POJFM/dmp-plant-hub/docs/final-report-sikora/img/web-ui-pump.png

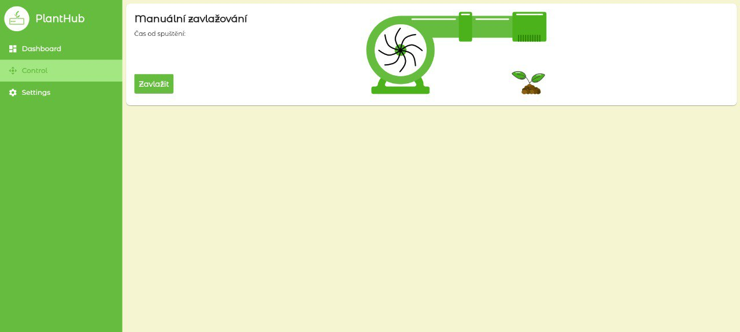
docs/final-report-sikora/img/web-ui-pump.png
