POJFM/dmp-plant-hub/docs/schemas/circuit-schema.png

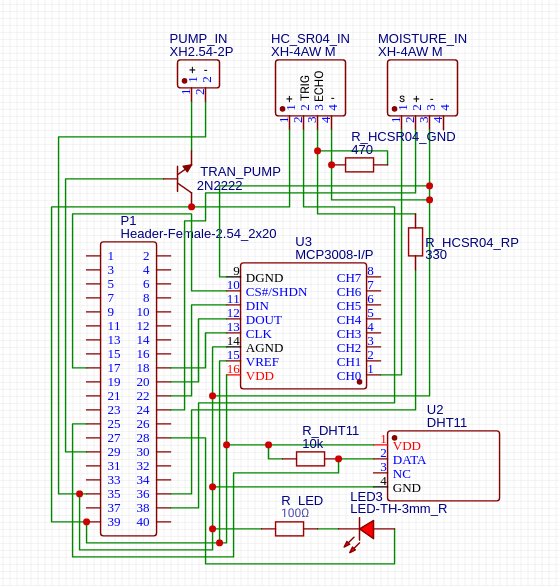
docs/schemas/circuit-schema.png
