POJFM/dmp-plant-hub/docs/schemas/circuit-traces.png

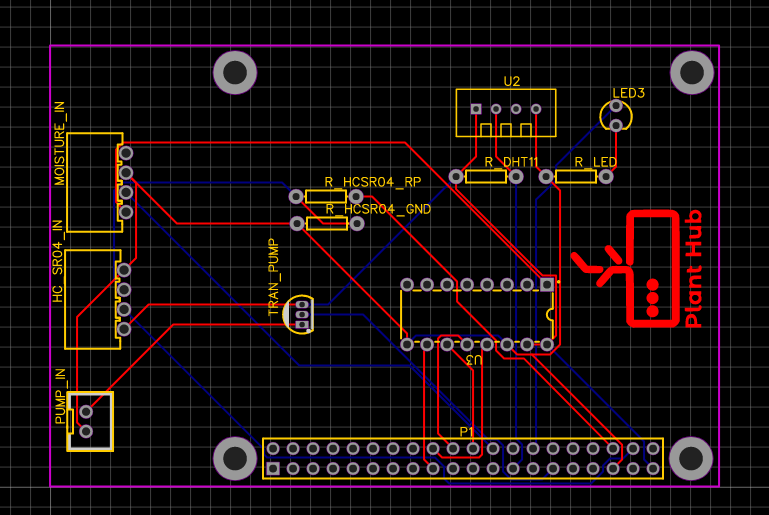
docs/schemas/circuit-traces.png
