POJFM/dmp-plant-hub/docs/schemas/circuit.png

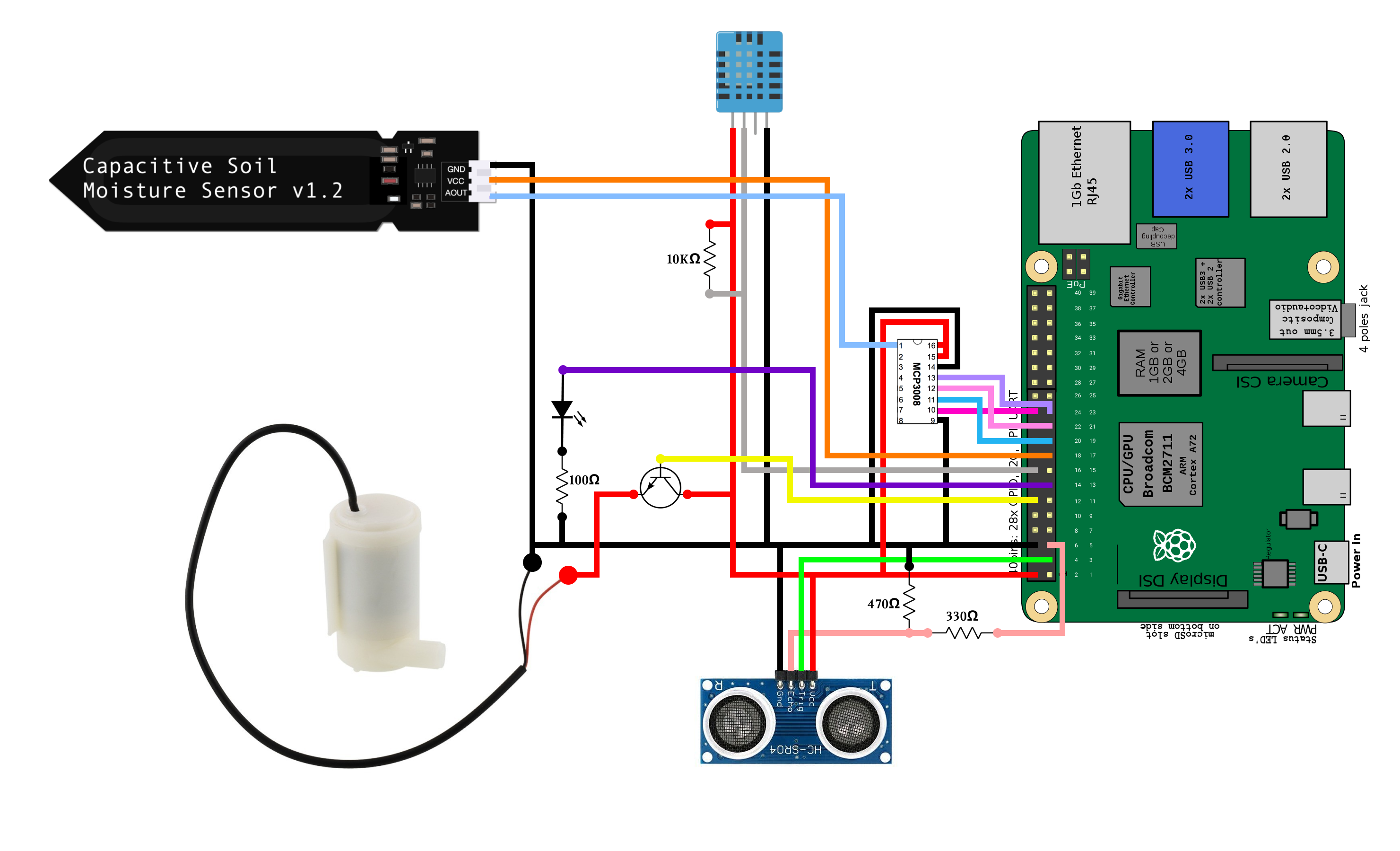
docs/schemas/circuit.png
